MinDans/RA-Sentinel/RASRF2400WBMC/Hardware/KiCad/ADC3244kicad_sch.kicad_sch

## KiCad design RASRF2400WBMC/Hardware/KiCad/ADC3244kicad_sch.kicad_sch (2026-04-13)

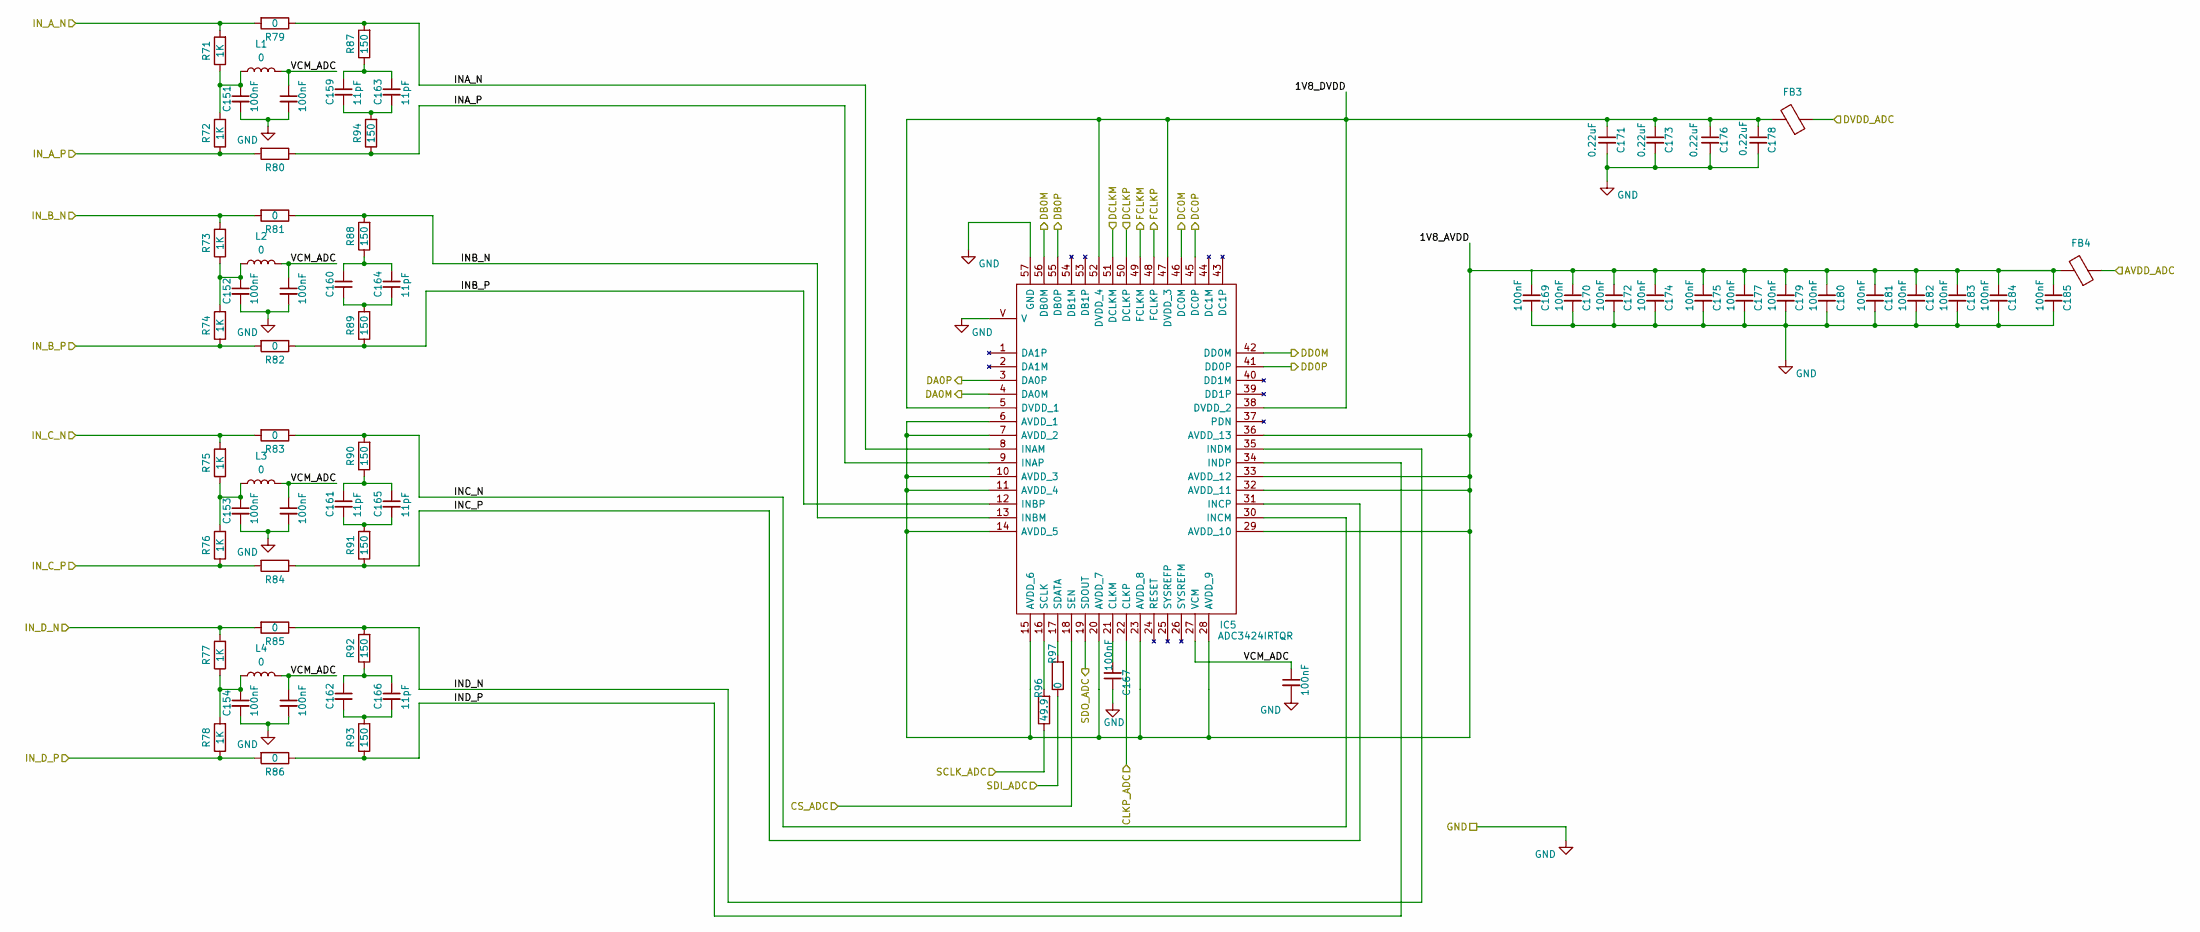
[picture p59: schematic ADC3244kicad_sch.kicad_sch]

Parts:
C151, C152, C153, C154, C155, C156, C157, C158: 100nF; C_0603_1608Metric; Manufacturer_Part_Number GRM188R71H104KA93D
C159, C160, C161, C162, C163, C164, C165, C166: 11pF; C_0402_1005Metric; Manufacturer_Part_Number 500R07S110GV4T
C167, C168, C169, C170, C172, C174, C175, C177, C179, C180, C181, C182, C183, C184, C185: 100nF; C_0402_1005Metric; Manufacturer_Part_Number GRM155R71A104KA01D
C171, C173, C176, C178: 0.22uF; C_0603_1608Metric; Manufacturer_Part_Number CC0603KRX7R9BB224
FB3, FB4: BLM41PG102SN1L; IND_BLM41_1806_MUR; Manufacturer_Part_Number BLM41PG102SN1L
IC5: ADC3424IRTQR; QFN50P800X800X100-57N-D; Mouser Part Number 595-ADC3424IRTQR
L1, L2, L3, L4: 0; L_0603_1608Metric; Manufacturer_Part_Number RC0603JR-070RL
R71, R72, R73, R74, R75, R76, R77, R78: 1K; R_0603_1608Metric; Manufacturer_Part_Number RC0603FR-071KL
R79, R80, R81, R82, R83, R84, R85, R86, R97: 0; R_0603_1608Metric; Manufacturer_Part_Number RC0603JR-070RL
R87, R88, R89, R90, R91, R92, R93, R94: 150; R_0603_1608Metric; Manufacturer_Part_Number RC0603FR-07150RL
R96: 49.9; R_0603_1608Metric; Manufacturer_Part_Number RC0603FR-0749R9L

Connections:
1V8_AVDD: C169.1, C170.1, C172.1, C174.1, C175.1, C177.1, C179.1, C180.1, C181.1, C182.1, C183.1, C184.1, C185.1, FB4.2, IC5.6 (AVDD_1), IC5.7 (AVDD_2), IC5.10 (AVDD_3), IC5.11 (AVDD_4), IC5.14 (AVDD_5), IC5.15 (AVDD_6), IC5.20 (AVDD_7), IC5.23 (AVDD_8), IC5.28 (AVDD_9), IC5.29 (AVDD_10), IC5.32 (AVDD_11), IC5.33 (AVDD_12), IC5.36 (AVDD_13)
1V8_DVDD: C171.1, C173.1, C176.1, C178.1, FB3.2, IC5.5 (DVDD_1), IC5.38 (DVDD_2), IC5.47 (DVDD_3), IC5.52 (DVDD_4)
AVDD_ADC: FB4.1
CLKP_ADC: IC5.22 (CLKP)
CS_ADC: IC5.18 (SEN)
DA0M: IC5.4 (DA0M)
DA0P: IC5.3 (DA0P)
DB0M: IC5.56 (DB0M)
DB0P: IC5.55 (DB0P)
DC0M: IC5.46 (DC0M)
DC0P: IC5.45 (DC0P)
DCLKM: IC5.51 (DCLKM)
DCLKP: IC5.50 (DCLKP)
DD0M: IC5.42 (DD0M)
DD0P: IC5.41 (DD0P)
DVDD_ADC: FB3.1
FCLKM: IC5.49 (FCLKM)
FCLKP: IC5.48 (FCLKP)
GND: C151.2, C152.2, C153.2, C154.2, C155.2, C156.2, C157.2, C158.2, C167.1, C168.2, C169.2, C170.2, C171.2, C172.2, C173.2, C174.2, C175.2, C176.2, C177.2, C178.2, C179.2, C180.2, C181.2, C182.2, C183.2, C184.2, C185.2, IC5.57 (GND), IC5.V
INA_N: IC5.8 (INAM), R79.1, R87.2
INA_P: IC5.9 (INAP), R80.1, R94.1
INB_N: IC5.13 (INBM), R81.1, R88.2
INB_P: IC5.12 (INBP), R82.1, R89.1
INC_N: IC5.30 (INCM), R83.1, R90.2
INC_P: IC5.31 (INCP), R84.1, R91.1
IND_N: IC5.35 (INDM), R85.1, R92.2
IND_P: IC5.34 (INDP), R86.1, R93.1
IN_A_N: R71.2, R79.2
IN_A_P: R72.1, R80.2
IN_B_N: R73.2, R81.2
IN_B_P: R74.1, R82.2
IN_C_N: R75.2, R83.2
IN_C_P: R76.1, R84.2
IN_D_N: R77.2, R85.2
IN_D_P: R78.1, R86.2
unnamed: C151.1, L1.1, R71.1, R72.2
unnamed: C152.1, L2.1, R73.1, R74.2
unnamed: C153.1, L3.1, R75.1, R76.2
unnamed: C154.1, L4.1, R77.1, R78.2
unnamed: C159.1, C163.1, R87.1
unnamed: C159.2, C163.2, R94.2
unnamed: C160.1, C164.1, R88.1
unnamed: C160.2, C164.2, R89.2
unnamed: C161.1, C165.1, R90.1
unnamed: C161.2, C165.2, R91.2
unnamed: C162.1, C166.1, R92.1
unnamed: C162.2, C166.2, R93.2
unnamed: C167.2, IC5.21 (CLKM)
unnamed: IC5.16 (SCLK), R96.2
unnamed: IC5.17 (SDATA), R97.2
SCLK_ADC: R96.1
SDI_ADC: R97.1
SDO_ADC: IC5.19 (SDOUT)
VCM_ADC: C155.1, C156.1, C157.1, C158.1, C168.1, IC5.27 (VCM), L1.2, L2.2, L3.2, L4.2
