MinDans/RA-Sentinel/RASRF2400WBMC/Hardware/KiCad/MAX2831.kicad_sch

## KiCad design RASRF2400WBMC/Hardware/KiCad/MAX2831.kicad_sch (2026-04-13)

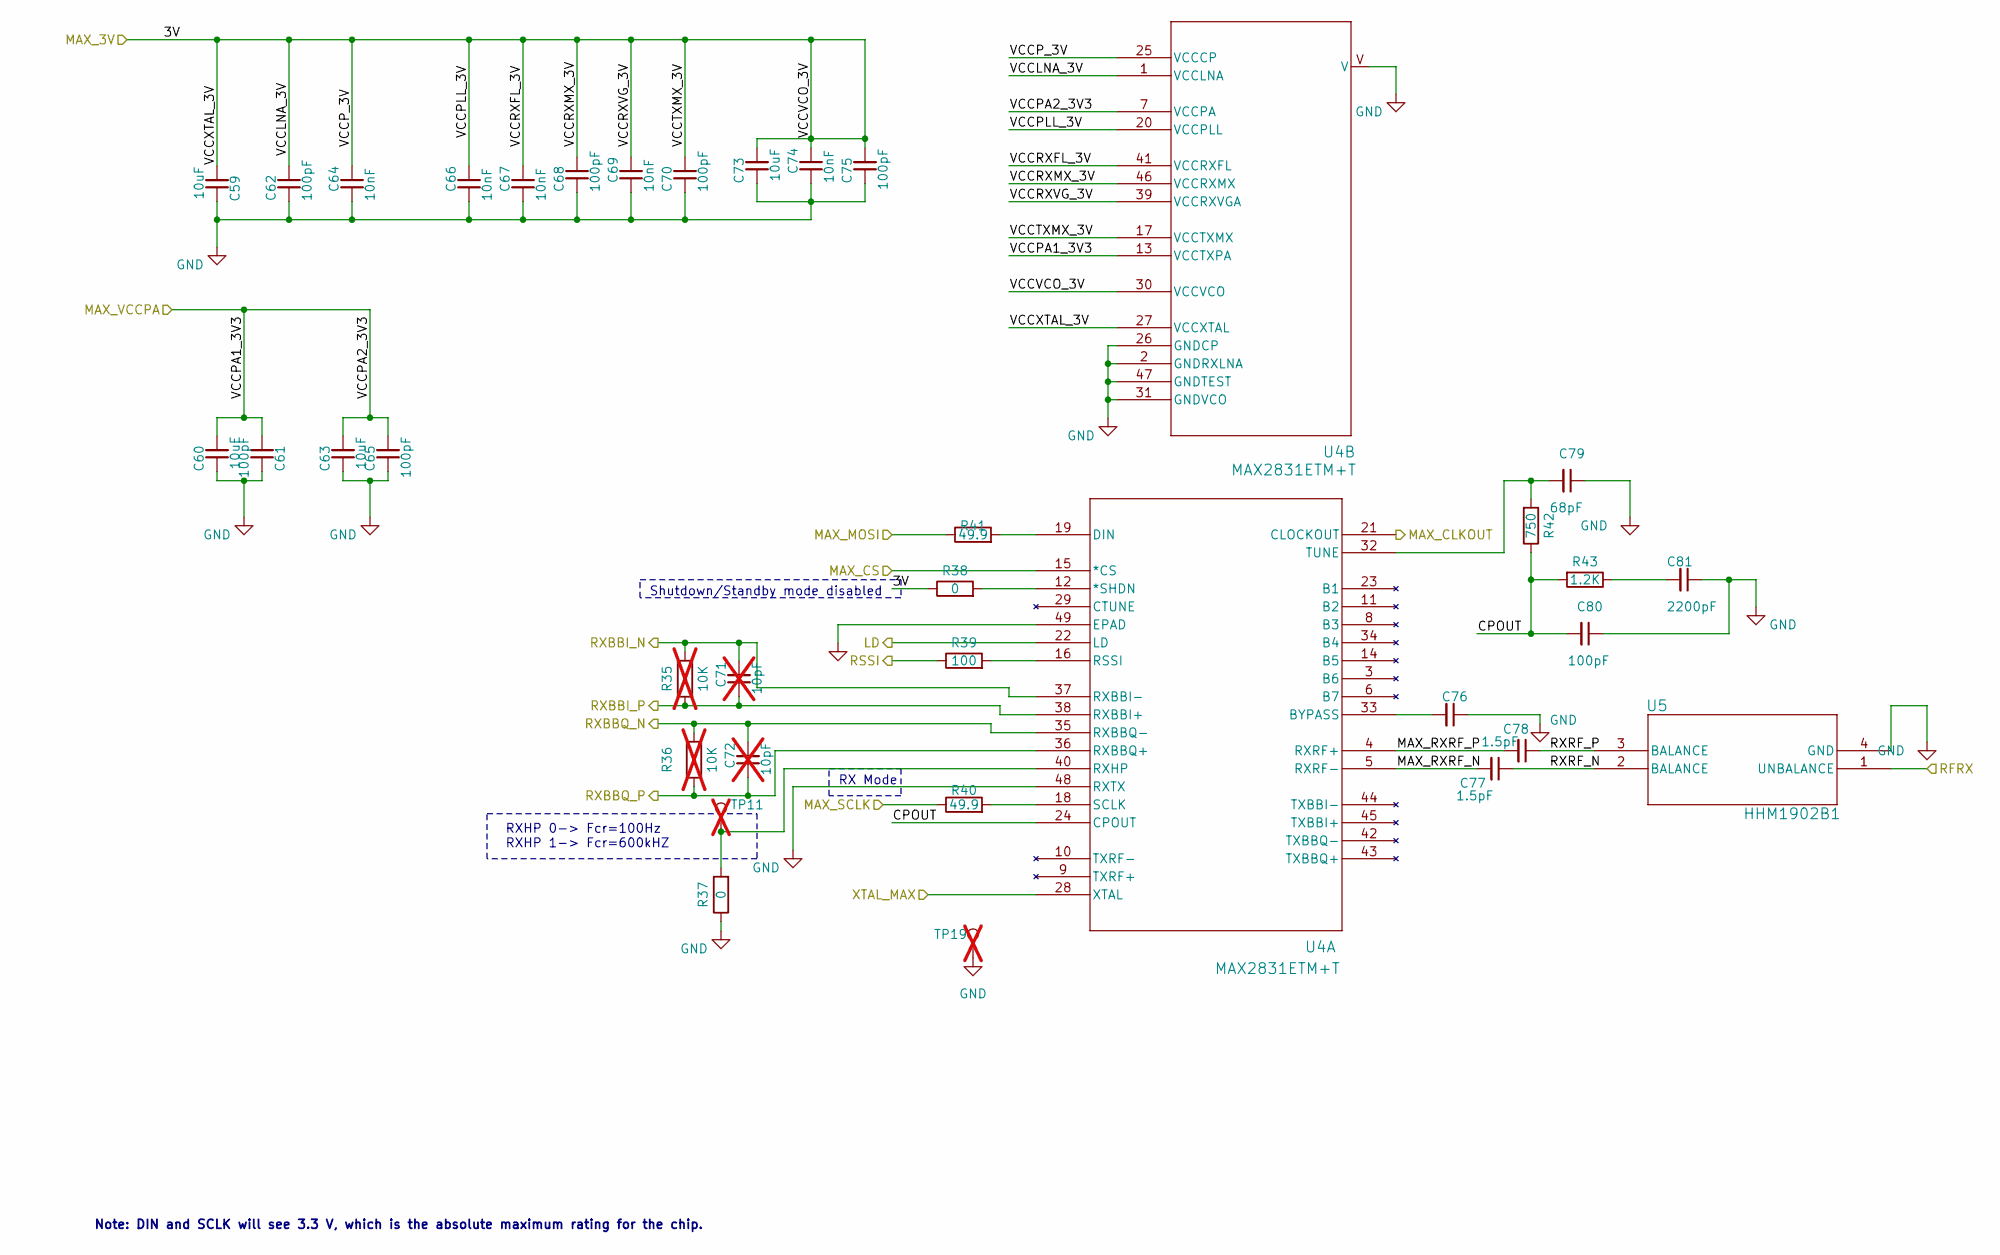
[picture p60: schematic MAX2831.kicad_sch]

Parts:
C59, C60, C63, C73: 10uF; C_0402_1005Metric; Manufacturer_Part_Number GRM155R61A106ME11D
C61, C62, C65, C68, C70, C75, C80: 100pF; C_0402_1005Metric; Manufacturer_Part_Number GRM1555C1H101JA01D
C64, C66, C67, C69, C74: 10nF; C_0402_1005Metric; Manufacturer_Part_Number GRM155R71H103KA88D
C71, C72: 10pF; C_0402_1005Metric; Manufacturer_Part_Number GRM1555C1H100JZ01D; not fitted
C76: 100nF; C_0402_1005Metric; Manufacturer_Part_Number GRM155R71A104KA01D
C77, C78: 1.5pF; C_0402_1005Metric; Manufacturer_Part_Number GJM1555C1H1R5BB01D
C79: 68pF; C_0402_1005Metric; Manufacturer_Part_Number GRM1555C1H680JZ01D
C81: 2200pF; C_0402_1005Metric; Manufacturer_Part_Number GRM1555C1H222JA01D
R35, R36: 10K; R_0402_1005Metric; Manufacturer_Part_Number RC0402FR-0710KL; not fitted
R37, R38: 0; R_0603_1608Metric; Manufacturer_Part_Number RC0603JR-070RL
R39: 100; R_0603_1608Metric; Manufacturer_Part_Number RC0603FR-07100RL
R40, R41: 49.9; R_0603_1608Metric; Manufacturer_Part_Number RC0603FR-0749R9L
R42: 750; R_0603_1608Metric; Manufacturer_Part_Number RC0603FR-07750RL
R43: 1.2K; R_0603_1608Metric; Manufacturer_Part_Number RC0603FR-071K2L
TP11: TestPoint; TestPoint_Pad_D1.0mm; not fitted
TP19: TestPoint; TestPoint_THTPad_D1.0mm_Drill0.5mm; not fitted
U4: MAX2831ETM+T; 21-0144_T4877&plus_4_MXM; Manufacturer_Part_Number MAX2831ETM+T
U5: HHM1902B1; HHM-4_1P0X0P5; Manufacturer_Part_Number HHM1902B1

Connections:
3V: C59.2, C62.1, C64.1, C66.1, C67.1, C68.1, C69.1, C70.1, C73.2, C74.1, C75.2, R38.1, U4.1 (VCCLNA), U4.17 (VCCTXMX), U4.20 (VCCPLL), U4.25 (VCCCP), U4.27 (VCCXTAL), U4.30 (VCCVCO), U4.39 (VCCRXVGA), U4.41 (VCCRXFL), U4.46 (VCCRXMX)
CPOUT: C80.2, R42.1, R43.2, U4.24 (CPOUT)
GND: C59.1, C60.1, C61.1, C62.2, C63.1, C64.2, C65.1, C66.2, C67.2, C68.2, C69.2, C70.2, C73.1, C74.2, C75.1, C76.1, C79.1, C80.1, C81.1, R37.1, TP19.1, U4.2 (GNDRXLNA), U4.26 (GNDCP), U4.31 (GNDVCO), U4.47 (GNDTEST), U4.48 (RXTX), U4.49 (EPAD), U4.V, U5.4 (GND)
LD: U4.22 (LD)
MAX_CLKOUT: U4.21 (CLOCKOUT)
MAX_CS: U4.15 (*CS)
MAX_MOSI: R41.1
MAX_RXRF_N: C77.2, U4.5 (RXRF-)
MAX_RXRF_P: C78.2, U4.4 (RXRF+)
MAX_SCLK: R40.1
MAX_VCCPA: C60.2, C61.2, C63.2, C65.2, U4.7 (VCCPA), U4.13 (VCCTXPA)
unnamed: C76.2, U4.33 (BYPASS)
unnamed: C79.2, R42.2, U4.32 (TUNE)
unnamed: C81.2, R43.1
unnamed: R37.2, TP11.1, U4.40 (RXHP)
unnamed: R38.2, U4.12 (*SHDN)
unnamed: R39.2, U4.16 (RSSI)
unnamed: R40.2, U4.18 (SCLK)
unnamed: R41.2, U4.19 (DIN)
RFRX: U5.1 (UNBALANCE)
RSSI: R39.1
RXBBI_N: C71.2, R35.2, U4.37 (RXBBI-)
RXBBI_P: C71.1, R35.1, U4.38 (RXBBI+)
RXBBQ_N: C72.2, R36.2, U4.35 (RXBBQ-)
RXBBQ_P: C72.1, R36.1, U4.36 (RXBBQ+)
RXRF_N: C77.1, U5.2 (BALANCE)
RXRF_P: C78.1, U5.3 (BALANCE)
XTAL_MAX: U4.28 (XTAL)

Notes on the sheet:
Shutdown/Standby mode disabled
Note: DIN and SCLK will see 3.3 V, which is the absolute maximum rating for the chip.
RXHP 0-> Fcr=100Hz RXHP 1-> Fcr=600kHZ
RX Mode
