MinDans/RA-Sentinel/RASRF2400WBMC/Hardware/KiCad/RASRF2400WBMC.kicad_sch

## KiCad design RASRF2400WBMC/Hardware/KiCad/RASRF2400WBMC.kicad_sch (2026-04-13)

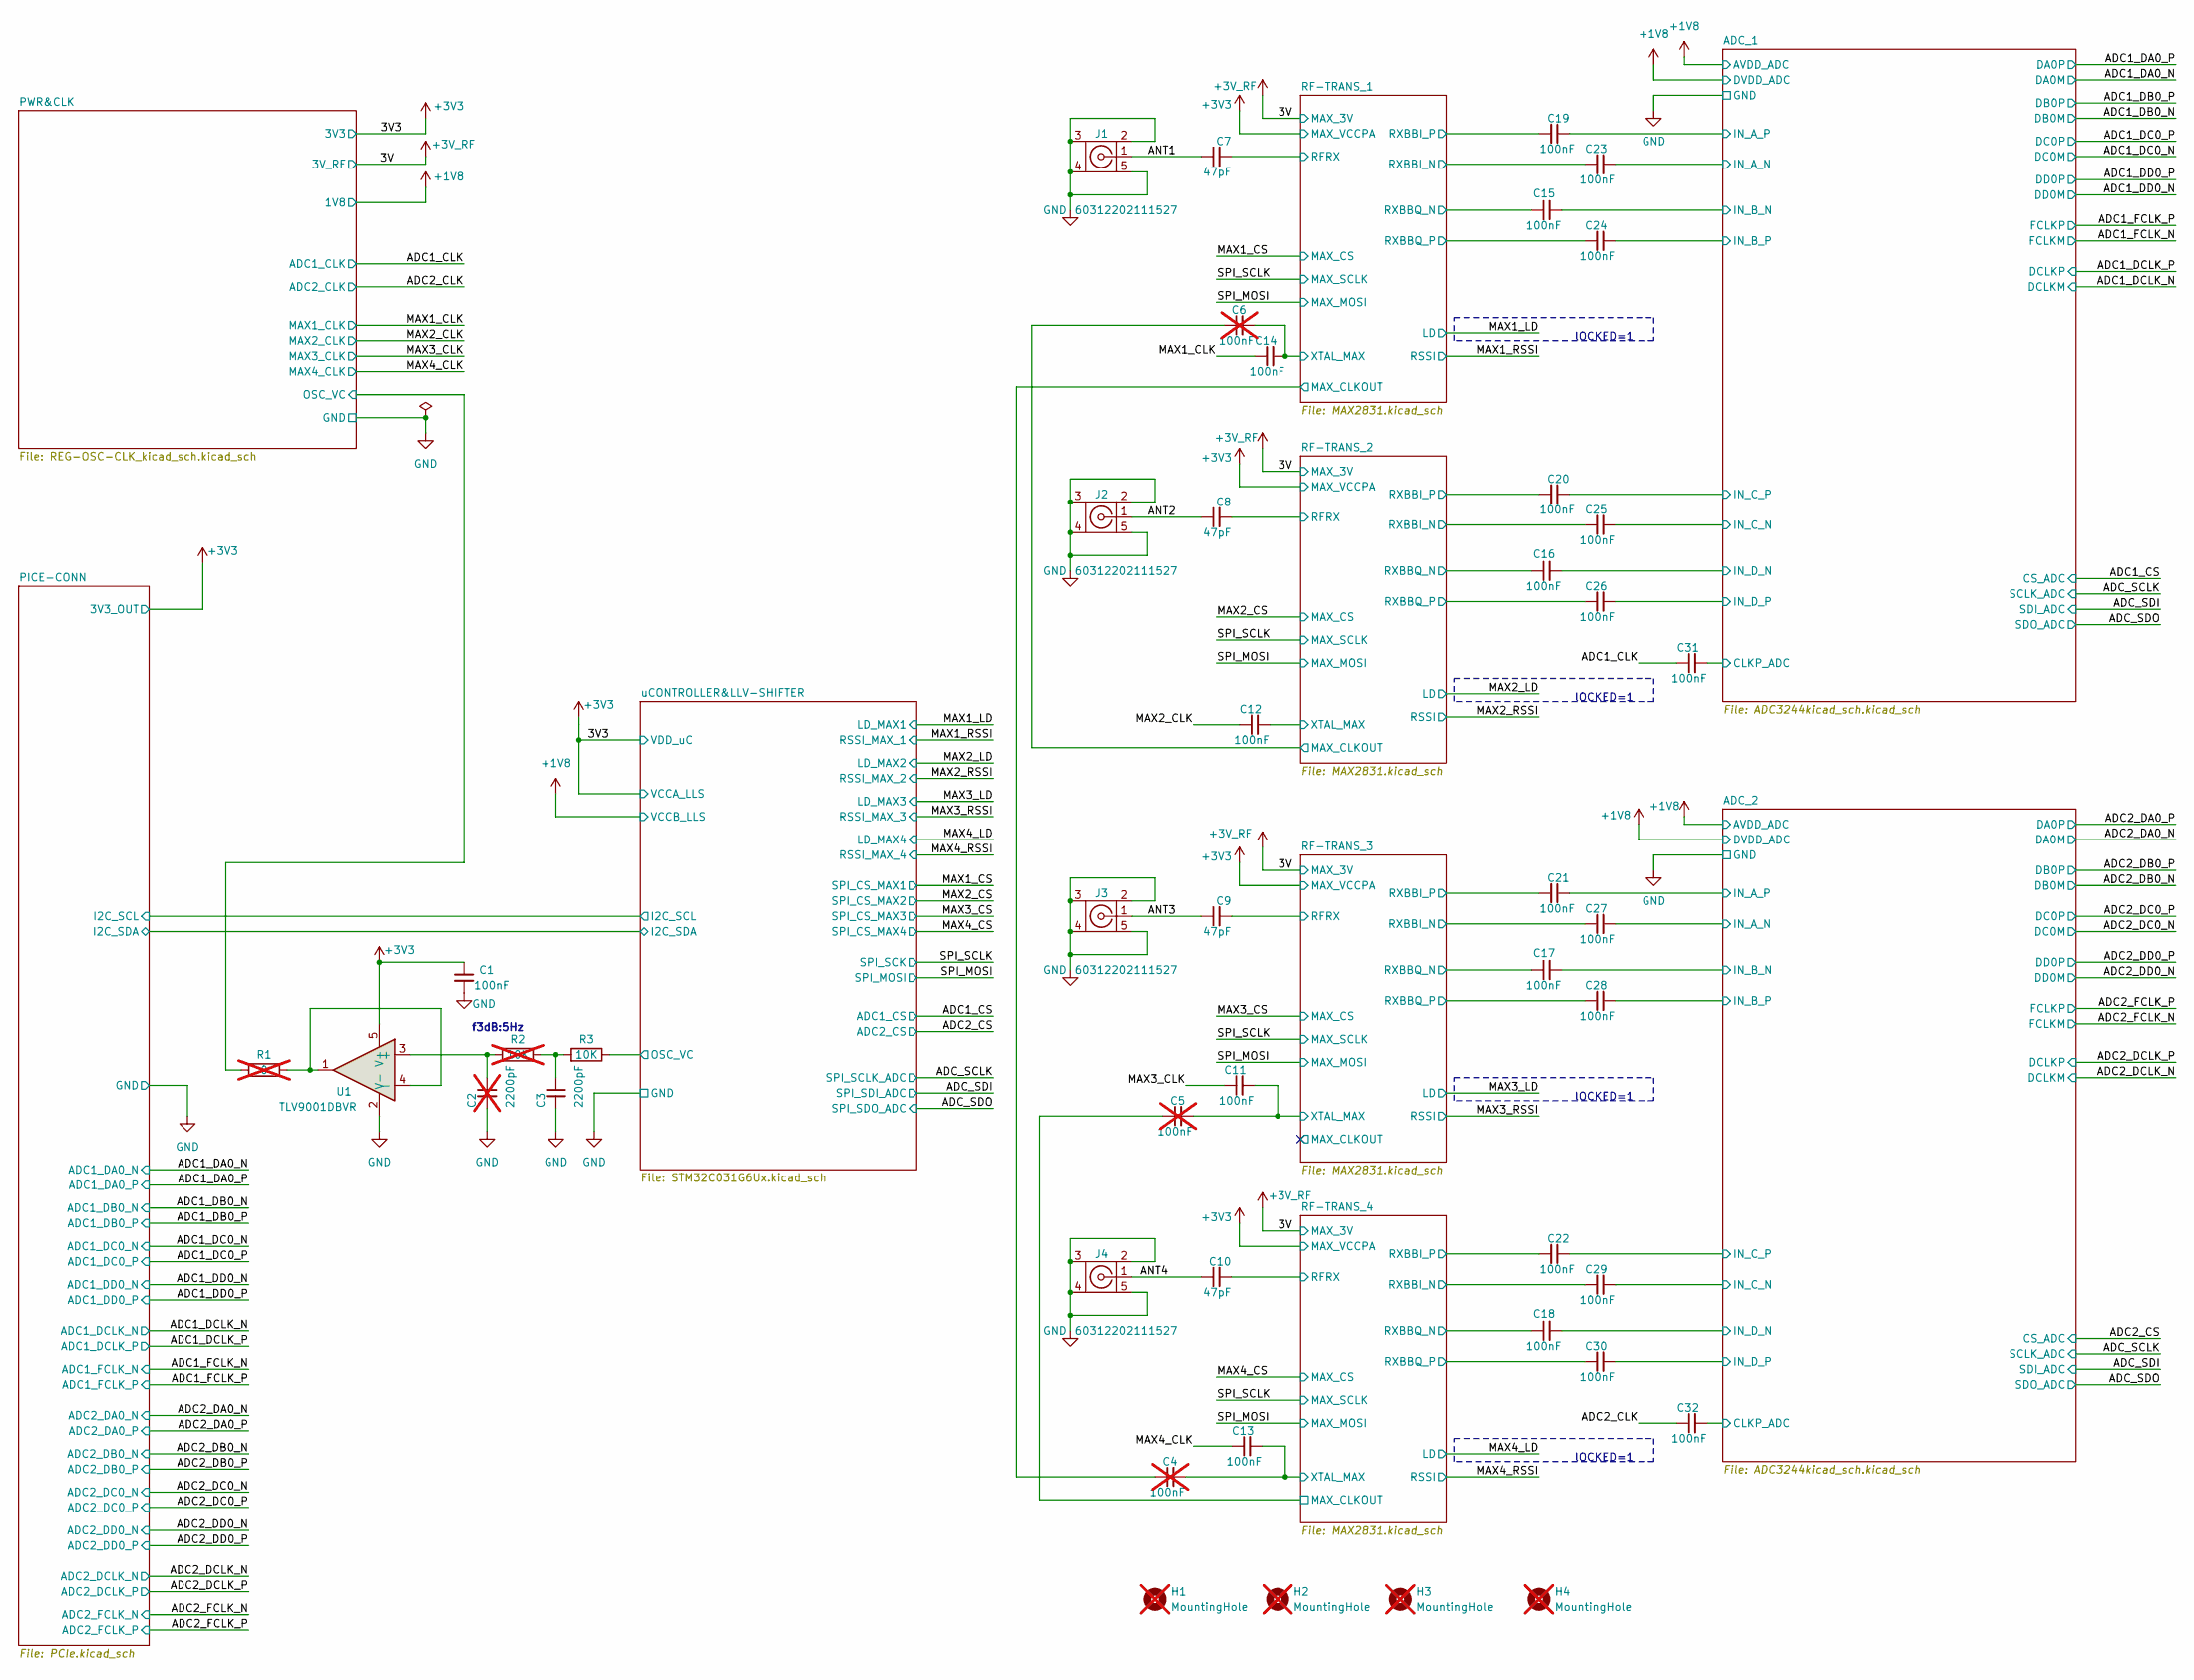
[picture p61: schematic RASRF2400WBMC.kicad_sch]

Parts:
C1, C11, C12, C13, C14, C15, C16, C17, C18, C19, C20, C21, C22, C23, C24, C25, C26, C27, C28, C29, C30, C31, C32: 100nF; C_0402_1005Metric; Manufacturer_Part_Number GRM155R71A104KA01D
C2: 2200pF; C_0402_1005Metric; Manufacturer_Part_Number GRM1555C1H222JA01D; not fitted
C3: 2200pF; C_0402_1005Metric; Manufacturer_Part_Number GRM1555C1H222JA01D
C4, C5, C6: 100nF; C_0603_1608Metric; Manufacturer_Part_Number GRM188R71H104KA93D; not fitted
C7, C8, C9, C10: 47pF; C_0402_1005Metric; Manufacturer_Part_Number GRM1555C1H470FA01D
H1, H2, H3, H4: MountingHole; MountingHole_3.2mm_M3_ISO7380; not fitted
J1, J2, J3, J4: 60312202111527; JACK_02114307_WRE; Manufacturer_Part_Number 60312202111527
R1: 0; R_0603_1608Metric; Manufacturer_Part_Number RC0603JR-070RL; not fitted
R2: 10K; R_0603_1608Metric; Manufacturer_Part_Number RC0603FR-0710KL; not fitted
R3: 10K; R_0603_1608Metric; Manufacturer_Part_Number RC0603FR-0710KL
U1: TLV9001DBVR; SOT-23-5; Manufacturer_Part_Number TLV9001DBVR

Connections:
+3V3: C1.1, U1.5 (V+)
ADC1_CLK: C31.1
ADC2_CLK: C32.1
ANT1: C7.1, J1.1
ANT2: C8.1, J2.1
ANT3: C9.1, J3.1
ANT4: C10.1, J4.1
CLKP_ADC: C31.2, C32.2
GND: C1.2, C2.2, C3.2, J1.2, J1.3, J1.4, J1.5, J2.2, J2.3, J2.4, J2.5, J3.2, J3.3, J3.4, J3.5, J4.2, J4.3, J4.4, J4.5, U1.2 (V-)
IN_A_N: C23.2, C27.2
IN_A_P: C19.1, C21.1
IN_B_N: C15.2, C17.2
IN_B_P: C24.2, C28.2
IN_C_N: C25.2, C29.2
IN_C_P: C20.1, C22.1
IN_D_N: C16.2, C18.2
IN_D_P: C26.2, C30.2
MAX1_CLK: C14.1
MAX2_CLK: C12.1
MAX3_CLK: C11.1
MAX4_CLK: C13.1
MAX_CLKOUT: C4.1, C5.1, C6.1
unnamed: C2.1, R2.1, U1.3 (+)
unnamed: C3.1, R2.2, R3.2
unnamed: R1.2, U1.1, U1.4 (-)
OSC_VC: R1.1, R3.1
RFRX: C7.2, C8.2, C9.2, C10.2
RXBBI_N: C23.1, C25.1, C27.1, C29.1
RXBBI_P: C19.2, C20.2, C21.2, C22.2
RXBBQ_N: C15.1, C16.1, C17.1, C18.1
RXBBQ_P: C24.1, C26.1, C28.1, C30.1
XTAL_MAX: C4.2, C5.2, C6.2, C11.2, C12.2, C13.2, C14.2

Notes on the sheet:
lOCKED=1
f3dB:5Hz
