MinDans/RA-Sentinel/RASRF2400WBMC/Hardware/KiCad/REG-OSC-CLK_kicad_sch.kicad_sch

## KiCad design RASRF2400WBMC/Hardware/KiCad/REG-OSC-CLK_kicad_sch.kicad_sch (2026-04-19)

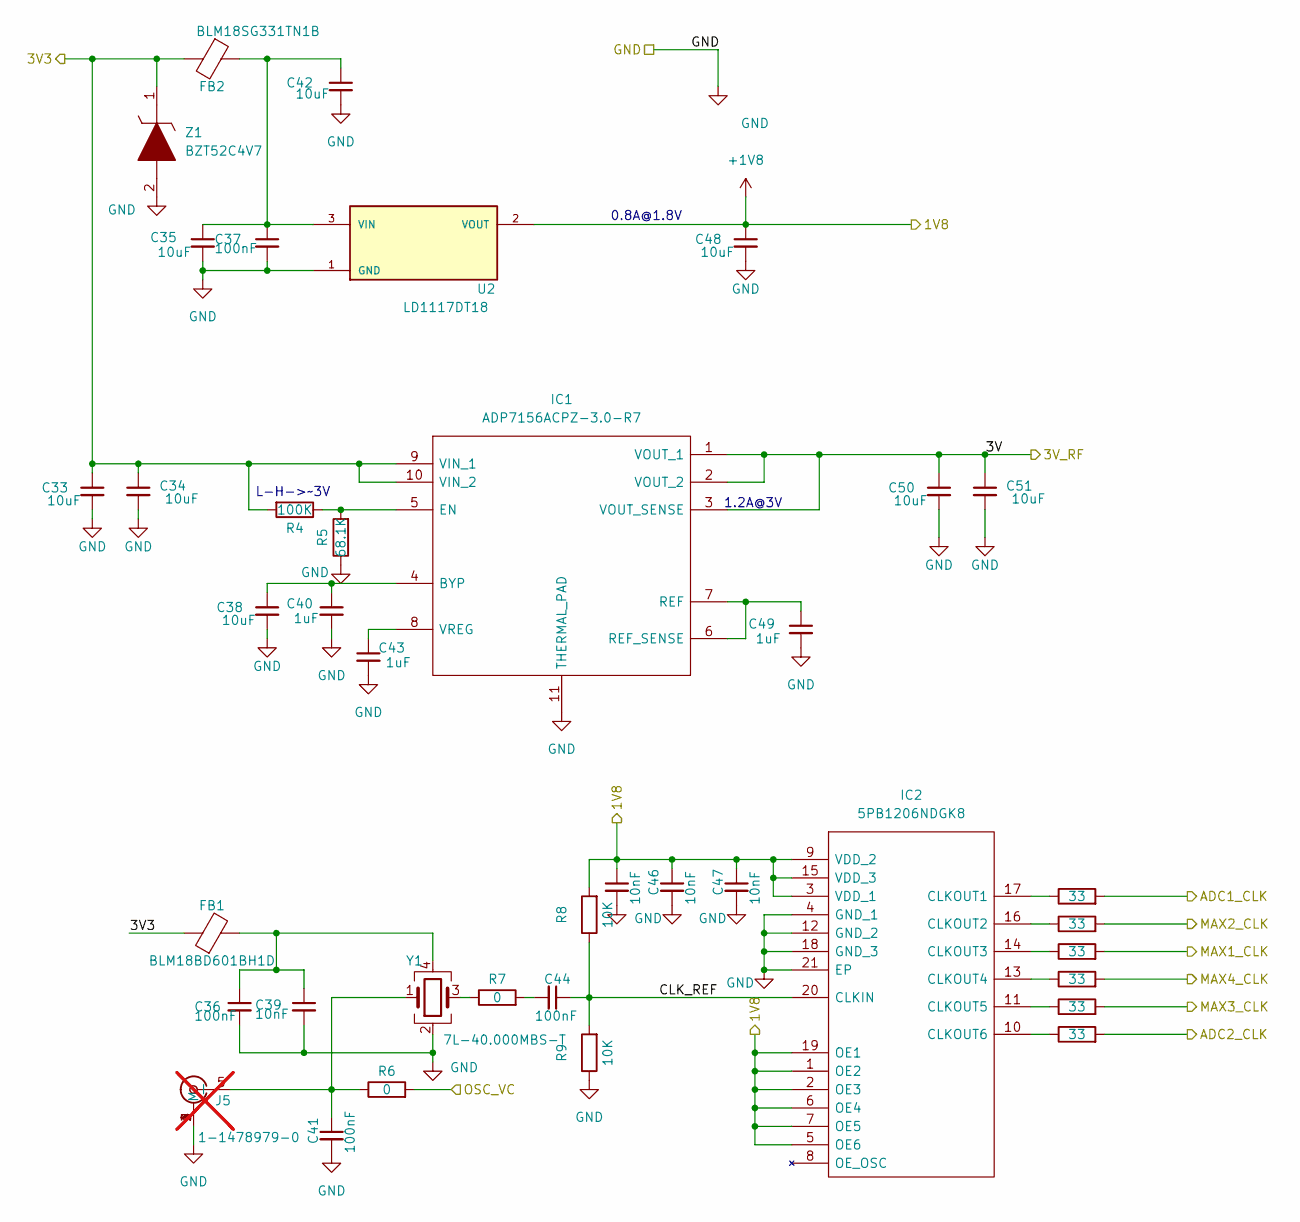
[picture p62: schematic REG-OSC-CLK_kicad_sch.kicad_sch]

Parts:
C33, C34, C35, C38, C42, C48, C50, C51: 10uF; C_0603_1608Metric; Manufacturer_Part_Number GRM188R61E106MA73D
C36, C41, C44: 100nF; C_0402_1005Metric; Manufacturer_Part_Number GRM155R71A104KA01D
C37: 100nF; C_0603_1608Metric; Manufacturer_Part_Number GRM188R71H104KA93D
C39, C45, C46, C47: 10nF; C_0402_1005Metric; Manufacturer_Part_Number GRM155R71H103KA88D
C40, C43, C49: 1uF; C_0603_1608Metric; Manufacturer_Part_Number GRM188R71E105KA12D
FB1: BLM18BD601BH1D; IND_BLM18_0603_MUR; Manufacturer_Part_Number BLM18BD601BH1D
FB2: BLM18SG331TN1B; IND_BLM18_0603_MUR; Manufacturer_Part_Number BLM18SG331TN1D
IC1: ADP7156ACPZ-3.0-R7; SON50P300X300X80-11N-D; Mouser Part Number 584-ADP7156ACPZ3.0R7
IC2: 5PB1206NDGK8; QFN40P300X300X100-21N-D; Mouser Part Number 972-5PB1206NDGK8
J5: 1-1478979-0; 114789790; Mouser Part Number 571-1-1478979-0; not fitted
R4: 100K; R_0603_1608Metric; Manufacturer_Part_Number RC0603FR-07100KL
R5: 68.1K; R_0603_1608Metric; Manufacturer_Part_Number RC0603FR-0768K1L
R6, R7: 0; R_0603_1608Metric; Manufacturer_Part_Number RC0603JR-070RL
R8: 10K; R_0603_1608Metric; Manufacturer_Part_Number RC0603FR-0710KL
R9: 10K; R_0402_1005Metric; Manufacturer_Part_Number RC0402FR-0710KL
R10, R11, R12, R13, R14, R15: 33; R_0603_1608Metric; Manufacturer_Part_Number RC0603FR-0733RL
U2: LD1117DT18; DPAK456P1010X240-3N; PARTREV 33
Y1: 7L-40.000MBS-T; 4-SMD_NoLead_Oscillator; Manufacturer_Part_Number 7L-40.000MBS-T
Z1: BZT52C4V7; Mouser Part Number 637-BZT52C4V7

Connections:
3V: C50.1, C51.1, IC1.1 (VOUT_1), IC1.2 (VOUT_2), IC1.3 (VOUT_SENSE)
3V3: C33.1, C34.1, FB1.1, FB2.2, IC1.9 (VIN_1), IC1.10 (VIN_2), R4.2, Z1.1
+1V8: C45.1, C46.1, C47.1, C48.1, IC2.1 (OE2), IC2.2 (OE3), IC2.3 (VDD_1), IC2.5 (OE6), IC2.6 (OE4), IC2.7 (OE5), IC2.9 (VDD_2), IC2.15 (VDD_3), IC2.19 (OE1), R8.2, U2.2 (VOUT)
ADC1_CLK: R11.2
ADC2_CLK: R15.2
CLK_REF: C44.1, IC2.20 (CLKIN), R8.1, R9.2
GND: C33.2, C34.2, C35.2, C36.2, C37.2, C38.2, C39.2, C40.2, C41.2, C42.2, C43.2, C45.2, C46.2, C47.2, C48.2, C49.2, C50.2, C51.2, IC1.11 (THERMAL_PAD), IC2.4 (GND_1), IC2.12 (GND_2), IC2.18 (GND_3), IC2.21 (EP), J5.1 (M), J5.2 (M), J5.3 (M), J5.4 (M), R5.1, R9.1, U2.1 (GND), Y1.2, Z1.2
MAX1_CLK: R12.2
MAX2_CLK: R10.2
MAX3_CLK: R14.2
MAX4_CLK: R13.2
unnamed: C35.1, C37.1, C42.1, FB2.1, U2.3 (VIN)
unnamed: C36.1, C39.1, FB1.2, Y1.4
unnamed: C38.1, C40.1, IC1.4 (BYP)
unnamed: C41.1, J5.5 (I), R6.1, Y1.1
unnamed: C43.1, IC1.8 (VREG)
unnamed: C44.2, R7.2
unnamed: C49.1, IC1.6 (REF_SENSE), IC1.7 (REF)
unnamed: IC1.5 (EN), R4.1, R5.2
unnamed: IC2.10 (CLKOUT6), R15.1
unnamed: IC2.11 (CLKOUT5), R14.1
unnamed: IC2.13 (CLKOUT4), R13.1
unnamed: IC2.14 (CLKOUT3), R12.1
unnamed: IC2.16 (CLKOUT2), R10.1
unnamed: IC2.17 (CLKOUT1), R11.1
unnamed: R7.1, Y1.3
OSC_VC: R6.2

Notes on the sheet:
0.8A@1.8V
L-H->~3V
1.2A@3V
