MinDans/RA-Sentinel/RASRF2400WBMC/Hardware/KiCad/STM32C031G6Ux.kicad_sch

## KiCad design RASRF2400WBMC/Hardware/KiCad/STM32C031G6Ux.kicad_sch (2026-04-13)

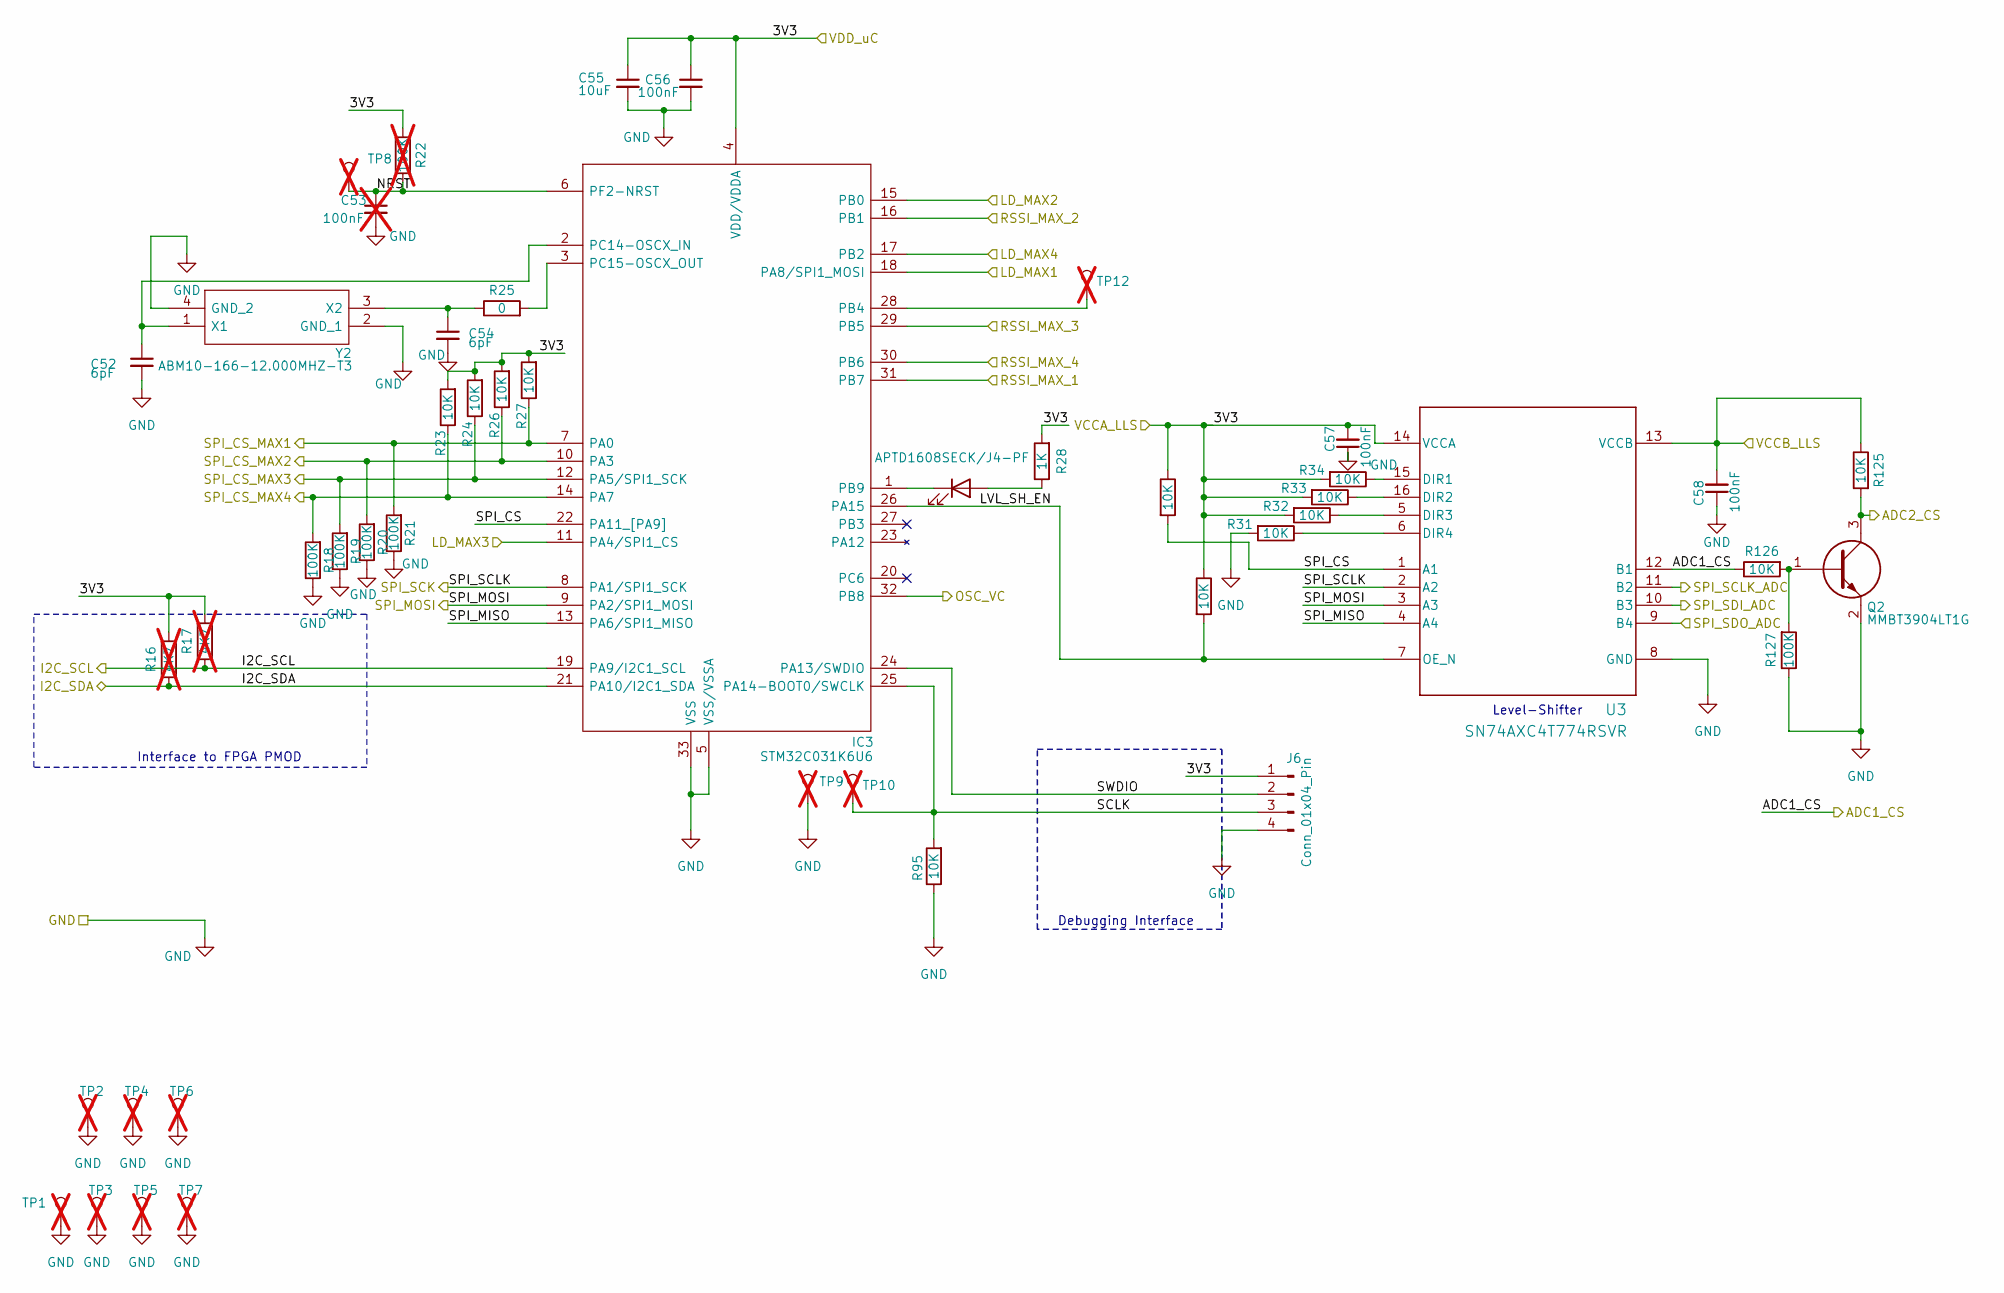
[picture p63: schematic STM32C031G6Ux.kicad_sch]

Parts:
C52, C54: 6pF; C_0402_1005Metric; Manufacturer_Part_Number GJM1555C1H6R0CB01D
C53: 100nF; C_0603_1608Metric; Manufacturer_Part_Number GRM188R71H104KA93D; not fitted
C55: 10uF; C_0402_1005Metric; Manufacturer_Part_Number GRM155R61A106ME11D
C56, C57, C58: 100nF; C_0402_1005Metric; Manufacturer_Part_Number GRM155R71A104KA01D
D1: APTD1608SECK/J4-PF; LED_0603_1608Metric; Manufacturer_Part_Number APTD1608SECK/J4-PF
IC3: STM32C031K6U6; QFN50P500X500X60-33N-D; Mouser Part Number 511-STM32C031K6U6
J6: Conn_01x04_Pin; PinSocket_1x04_P2.54mm_Vertical; Manufacturer_Part_Number TSW-104-07-G-S
Q2: MMBT3904LT1G; SOT96P237X111-3N; Mouser Part Number 863-MMBT3904LT1G
R16, R17: 4K7; R_0402_1005Metric; Manufacturer_Part_Number RC0402FR-074K7L; not fitted
R18, R19, R20, R21, R127: 100K; R_0402_1005Metric; Manufacturer_Part_Number RC0402FR-074K7L
R22: 100K; R_0603_1608Metric; Manufacturer_Part_Number RC0603FR-07100KL; not fitted
R23, R24, R26, R27, R29, R30, R31, R32, R33, R34, R95, R125, R126: 10K; R_0402_1005Metric; Manufacturer_Part_Number RC0402FR-0710KL
R25: 0; R_0603_1608Metric; Manufacturer_Part_Number RC0603JR-070RL
R28: 1K; R_0603_1608Metric; Manufacturer_Part_Number RC0603FR-071KL
TP1, TP2, TP3, TP4, TP5, TP6, TP7, TP9, TP10, TP12: TestPoint; TestPoint_THTPad_D1.0mm_Drill0.5mm; not fitted
TP8: TestPoint; TestPoint_Pad_1.0x1.0mm; not fitted
U3: SN74AXC4T774RSVR; RSV0016A; Manufacturer_Part_Number SN74AXC4T774RSVR
Y2: ABM10-166-12.000MHZ-T3; ABM10; Mouser Part Number 815-ABM10-166-12T

Connections:
3V3: C55.1, C56.1, C57.2, IC3.4 (VDD/VDDA), J6.1, R16.2, R17.1, R22.1, R23.2, R24.2, R26.2, R27.2, R28.2, R29.1, R30.1, R32.2, R33.2, R34.2, U3.14 (VCCA)
ADC1_CS: R126.1, U3.12 (B1)
ADC2_CS: Q2.3, R125.2
GND: C52.2, C53.2, C54.2, C55.2, C56.2, C57.1, C58.1, IC3.5 (VSS/VSSA), IC3.33 (VSS), J6.4, Q2.2, R18.1, R19.1, R20.1, R21.1, R31.2, R95.1, R127.1, TP1.1, TP2.1, TP3.1, TP4.1, TP5.1, TP6.1, TP7.1, TP9.1, U3.8 (GND), Y2.2 (GND_1), Y2.4 (GND_2)
I2C_SCL: IC3.19 (PA9/I2C1_SCL), R17.2
I2C_SDA: IC3.21 (PA10/I2C1_SDA), R16.1
LD_MAX1: IC3.18 (PA8/SPI1_MOSI)
LD_MAX2: IC3.15 (PB0)
LD_MAX3: IC3.11 (PA4/SPI1_CS)
LD_MAX4: IC3.17 (PB2)
LVL_SH_EN: IC3.26 (PA15), R30.2, U3.7 (OE_N)
NRST: C53.1, IC3.6 (PF2-NRST), R22.2, TP8.1
unnamed: C52.1, IC3.2 (PC14-OSCX_IN), Y2.1 (X1)
unnamed: C54.1, R25.1, Y2.3 (X2)
unnamed: D1.1 (K), IC3.1 (PB9)
unnamed: D1.2 (A), R28.1
unnamed: IC3.3 (PC15-OSCX_OUT), R25.2
unnamed: IC3.28 (PB4), TP12.1
unnamed: Q2.1, R126.2, R127.2
unnamed: R31.1, U3.6 (DIR4)
unnamed: R32.1, U3.5 (DIR3)
unnamed: R33.1, U3.16 (DIR2)
unnamed: R34.1, U3.15 (DIR1)
OSC_VC: IC3.32 (PB8)
RSSI_MAX_1: IC3.31 (PB7)
RSSI_MAX_2: IC3.16 (PB1)
RSSI_MAX_3: IC3.29 (PB5)
RSSI_MAX_4: IC3.30 (PB6)
SCLK: IC3.25 (PA14-BOOT0/SWCLK), J6.3, R95.2, TP10.1
SPI_CS: IC3.22 (PA11_[PA9]), R29.2, U3.1 (A1)
SPI_CS_MAX1: IC3.7 (PA0), R21.2, R27.1
SPI_CS_MAX2: IC3.10 (PA3), R20.2, R26.1
SPI_CS_MAX3: IC3.12 (PA5/SPI1_SCK), R19.2, R24.1
SPI_CS_MAX4: IC3.14 (PA7), R18.2, R23.1
SPI_MISO: IC3.13 (PA6/SPI1_MISO), U3.4 (A4)
SPI_MOSI: IC3.9 (PA2/SPI1_MOSI), U3.3 (A3)
SPI_SCK: IC3.8 (PA1/SPI1_SCK), U3.2 (A2)
SPI_SCLK_ADC: U3.11 (B2)
SPI_SDI_ADC: U3.10 (B3)
SPI_SDO_ADC: U3.9 (B4)
SWDIO: IC3.24 (PA13/SWDIO), J6.2
VCCB_LLS: C58.2, R125.1, U3.13 (VCCB)

Notes on the sheet:
Level-Shifter
Interface to FPGA PMOD
Debugging Interface
